nm47/FlywheelCube/CAD/STL/Backplate.stl

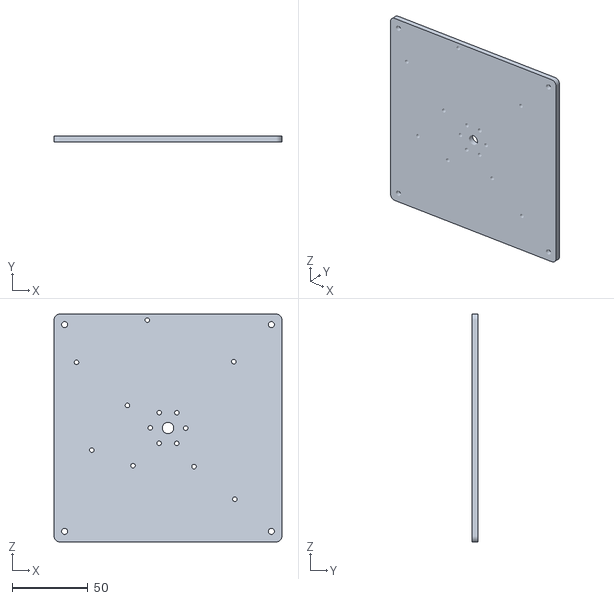
[picture p16: CAD file, 2020-06-09]
CAD/STL/Backplate.stl
150.0 x 4.00 x 150.0
